Freire-Elias/Astro-Core_PCB/docs/schematic/Alimentação.kicad_sch

## KiCad design docs/schematic/Alimentação.kicad_sch (2026-02-14)

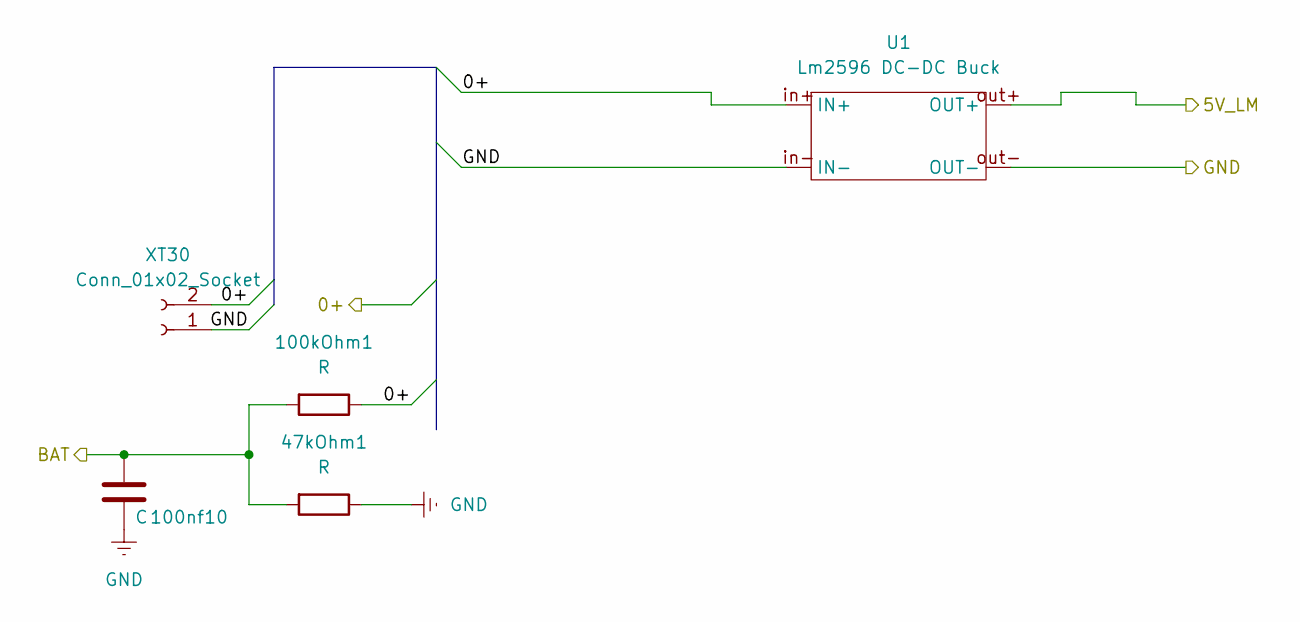
[picture p5: schematic Alimentação.kicad_sch]

Parts:
47kOhm1, 100kOhm1: R; R_Axial_DIN0207_L6.3mm_D2.5mm_P7.62mm_Horizontal
100nf10: C; C_Disc_D3.0mm_W1.6mm_P2.50mm
U1: Lm2596 DC-DC Buck; Lm2596_ALT
XT30: Conn_01x02_Socket; AMASS_XT30U-M_1x02_P5.0mm_Vertical

Connections:
0+: 100kOhm1.1, U1.in+ (IN+), XT30.2
5V_LM: U1.out+ (OUT+)
BAT: 47kOhm1.2, 100kOhm1.2, 100nf10.1
GND: 47kOhm1.1, 100nf10.2, U1.in- (IN-), U1.out- (OUT-), XT30.1
