Freire-Elias/Astro-Core_PCB/docs/schematic/AntaresMainV6.kicad_sch

## KiCad design docs/schematic/AntaresMainV6.kicad_sch (2026-02-14)

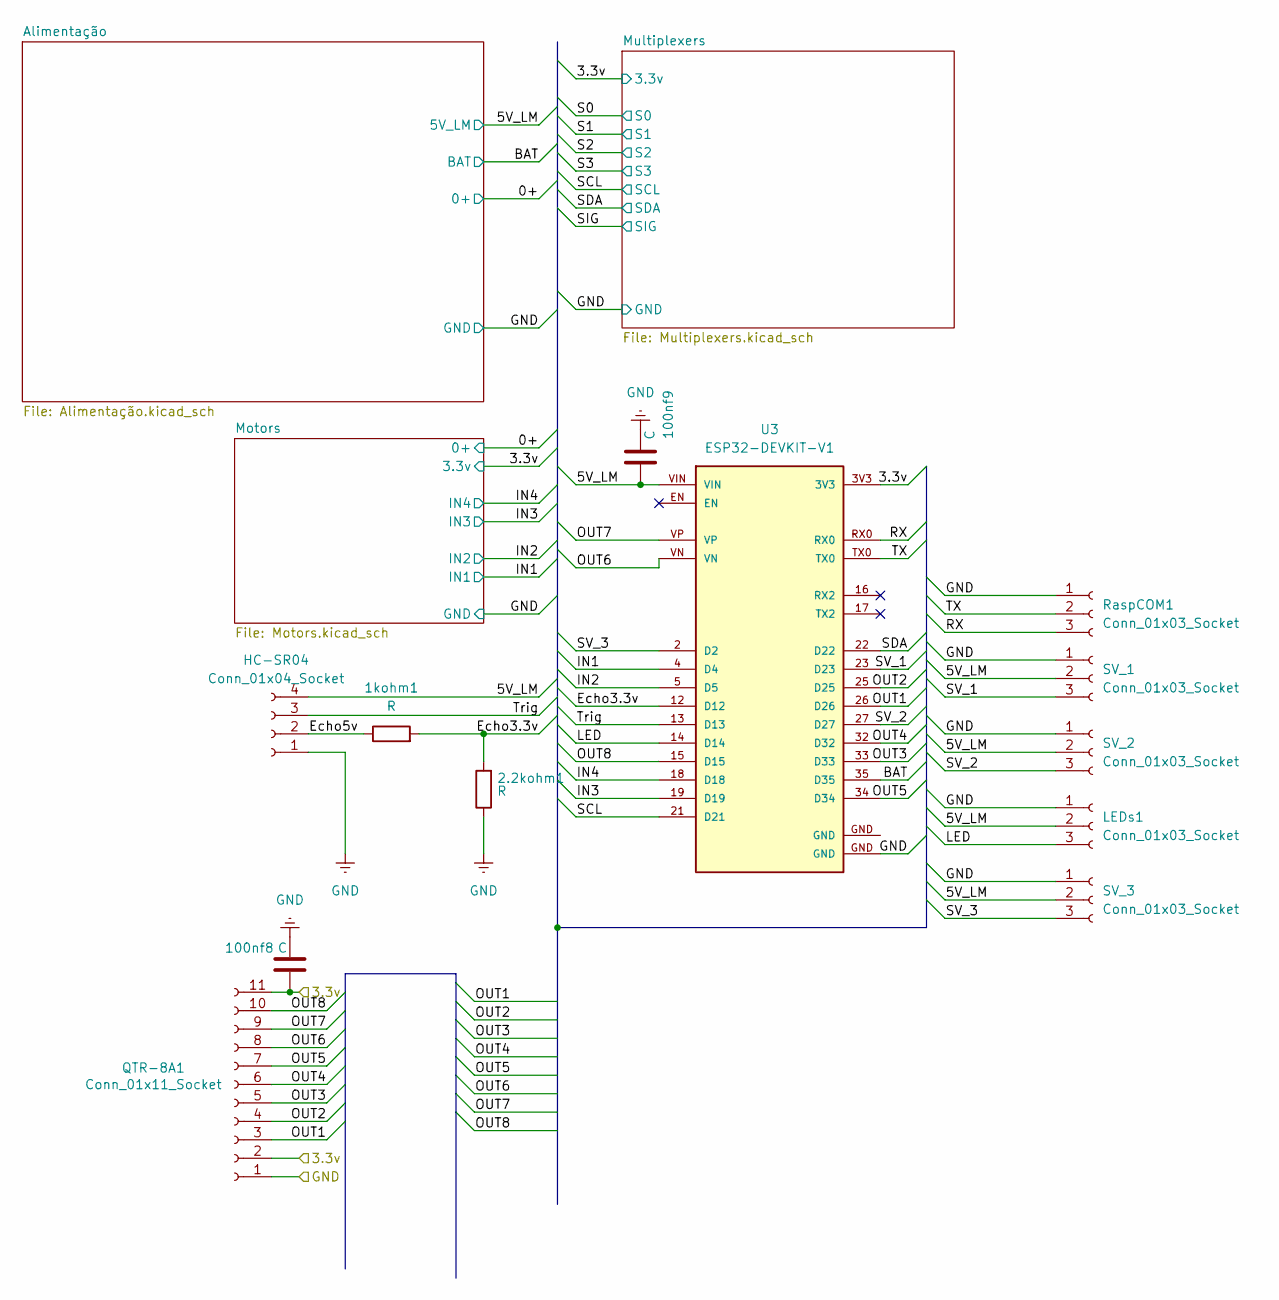
[picture p6: schematic AntaresMainV6.kicad_sch]

Parts:
1kohm1, 2.2kohm1: R; R_Axial_DIN0207_L6.3mm_D2.5mm_P7.62mm_Horizontal
100nf8, 100nf9: C; C_Disc_D3.0mm_W1.6mm_P2.50mm
HC-SR04: Conn_01x04_Socket; JST_XH_B4B-XH-A_1x04_P2.50mm_Vertical
LEDs1: Conn_01x03_Socket; JST_XH_B3B-XH-A_1x03_P2.50mm_Vertical
QTR-8A1: Conn_01x11_Socket; JST_XH_B11B-XH-A_1x11_P2.50mm_Vertical
RaspCOM1: Conn_01x03_Socket; JST_XH_B3B-XH-A_1x03_P2.50mm_Vertical
SV_1, SV_2, SV_3: Conn_01x03_Socket; JST_XH_B3B-XH-A_1x03_P2.50mm_Vertical
U3: ESP32-DEVKIT-V1; MODULE_ESP32_DEVKIT_V1; PARTREV N/A

Connections:
3.3v: 100nf8.1, QTR-8A1.2, QTR-8A1.11, U3.3V3
5V_LM: 100nf9.2, HC-SR04.4, LEDs1.2, SV_1.2, SV_2.2, SV_3.2, U3.VIN
BAT: U3.35 (D35)
Echo3.3v: 1kohm1.2, 2.2kohm1.2, U3.12 (D12)
Echo5v: 1kohm1.1, HC-SR04.2
GND: 2.2kohm1.1, 100nf8.2, 100nf9.1, HC-SR04.1, LEDs1.1, QTR-8A1.1, RaspCOM1.1, SV_1.1, SV_2.1, SV_3.1, U3.29 (GND), U3.GND
IN1: U3.4 (D4)
IN2: U3.5 (D5)
IN3: U3.19 (D19)
IN4: U3.18 (D18)
LED: LEDs1.3, U3.14 (D14)
OUT1: QTR-8A1.3, U3.26 (D26)
OUT2: QTR-8A1.4, U3.25 (D25)
OUT3: QTR-8A1.5, U3.33 (D33)
OUT4: QTR-8A1.6, U3.32 (D32)
OUT5: QTR-8A1.7, U3.34 (D34)
OUT6: QTR-8A1.8, U3.VN
OUT7: QTR-8A1.9, U3.VP
OUT8: QTR-8A1.10, U3.15 (D15)
RX: RaspCOM1.3, U3.RX0
SCL: U3.21 (D21)
SDA: U3.22 (D22)
SV_1: SV_1.3, U3.23 (D23)
SV_2: SV_2.3, U3.27 (D27)
SV_3: SV_3.3, U3.2 (D2)
TX: RaspCOM1.2, U3.TX0
Trig: HC-SR04.3, U3.13 (D13)
