Freire-Elias/Astro-Core_PCB/docs/schematic/Motors.kicad_sch

## KiCad design docs/schematic/Motors.kicad_sch (2026-02-14)

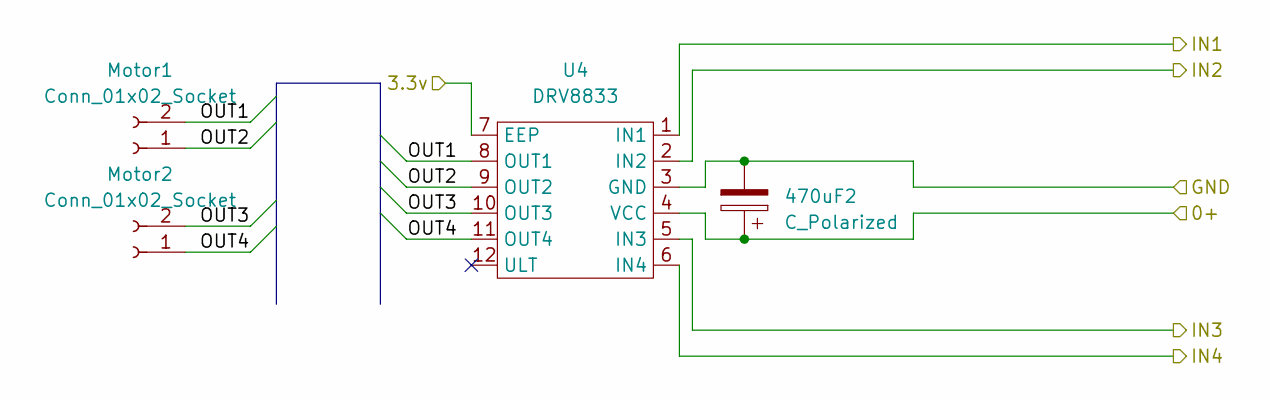
[picture p7: schematic Motors.kicad_sch]

Parts:
470uF2: C_Polarized; CP_Radial_D10.0mm_P3.50mm
Motor1, Motor2: Conn_01x02_Socket; JST_XH_B2B-XH-A_1x02_P2.50mm_Vertical
U4: DRV8833

Connections:
0+: 470uF2.1, U4.4 (VCC)
3.3v: U4.7 (EEP)
GND: 470uF2.2, U4.3 (GND)
IN1: U4.1 (IN1)
IN2: U4.2 (IN2)
IN3: U4.5 (IN3)
IN4: U4.6 (IN4)
OUT1: Motor1.2, U4.8 (OUT1)
OUT2: Motor1.1, U4.9 (OUT2)
OUT3: Motor2.2, U4.10 (OUT3)
OUT4: Motor2.1, U4.11 (OUT4)
