Freire-Elias/Astro-Core_PCB/docs/schematic/Multiplexers.kicad_sch

## KiCad design docs/schematic/Multiplexers.kicad_sch (2026-02-14)

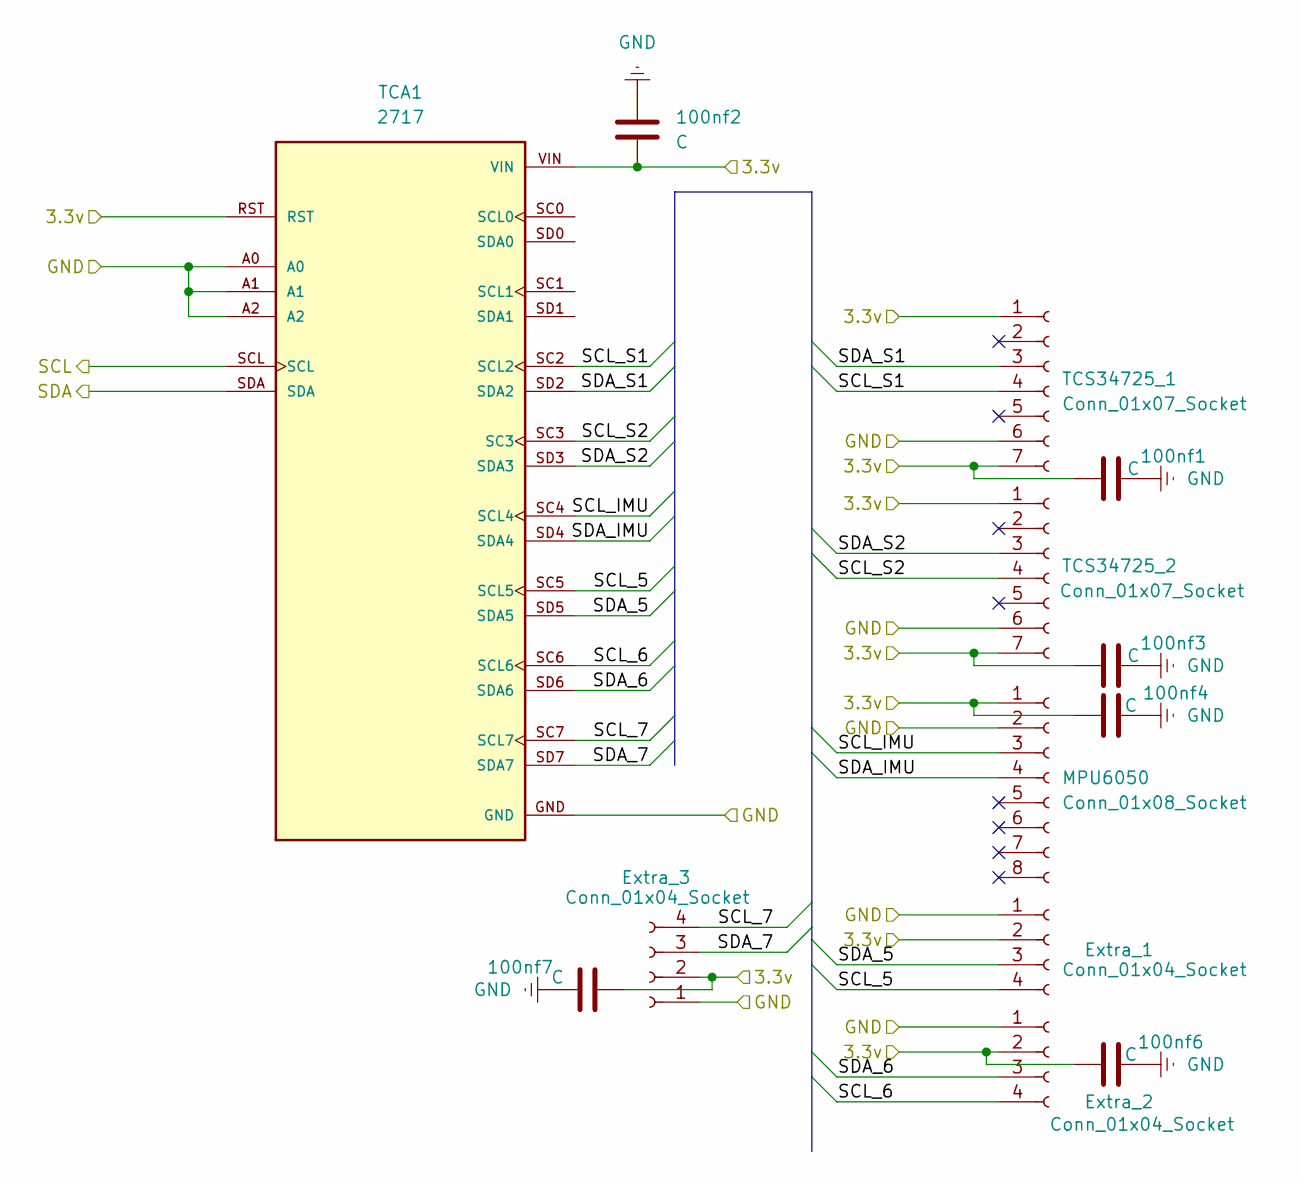
[picture p8: schematic Multiplexers.kicad_sch]

Parts:
100nf1, 100nf2, 100nf3, 100nf4, 100nf6, 100nf7: C; C_Disc_D3.0mm_W1.6mm_P2.50mm
Extra_1, Extra_2, Extra_3: Conn_01x04_Socket; JST_XH_B4B-XH-A_1x04_P2.50mm_Vertical
MPU6050: Conn_01x08_Socket; JST_XH_B8B-XH-A_1x08_P2.50mm_Vertical
TCA1: 2717; TCA9548_ALT; PARTREV Sep 11, 2015
TCS34725_1, TCS34725_2: Conn_01x07_Socket; JST_XH_B7B-XH-A_1x07_P2.50mm_Vertical

Connections:
3.3v: 100nf1.1, 100nf2.2, 100nf3.1, 100nf4.1, 100nf6.1, 100nf7.2, Extra_1.2, Extra_2.2, Extra_3.2, MPU6050.1, TCA1.RST, TCA1.VIN, TCS34725_1.1, TCS34725_1.7, TCS34725_2.1, TCS34725_2.7
GND: 100nf1.2, 100nf2.1, 100nf3.2, 100nf4.2, 100nf6.2, 100nf7.1, Extra_1.1, Extra_2.1, Extra_3.1, MPU6050.2, TCA1.A0, TCA1.A1, TCA1.A2, TCA1.GND, TCS34725_1.6, TCS34725_2.6
SCL: TCA1.SCL
SCL_5: Extra_1.4, TCA1.SC5 (SCL5)
SCL_6: Extra_2.4, TCA1.SC6 (SCL6)
SCL_7: Extra_3.4, TCA1.SC7 (SCL7)
SCL_IMU: MPU6050.3, TCA1.SC4 (SCL4)
SCL_S1: TCA1.SC2 (SCL2), TCS34725_1.4
SCL_S2: TCA1.SC3, TCS34725_2.4
SDA: TCA1.SDA
SDA_5: Extra_1.3, TCA1.SD5 (SDA5)
SDA_6: Extra_2.3, TCA1.SD6 (SDA6)
SDA_7: Extra_3.3, TCA1.SD7 (SDA7)
SDA_IMU: MPU6050.4, TCA1.SD4 (SDA4)
SDA_S1: TCA1.SD2 (SDA2), TCS34725_1.3
SDA_S2: TCA1.SD3 (SDA3), TCS34725_2.3
